quix12345/Q-Flight/qflight/12.png

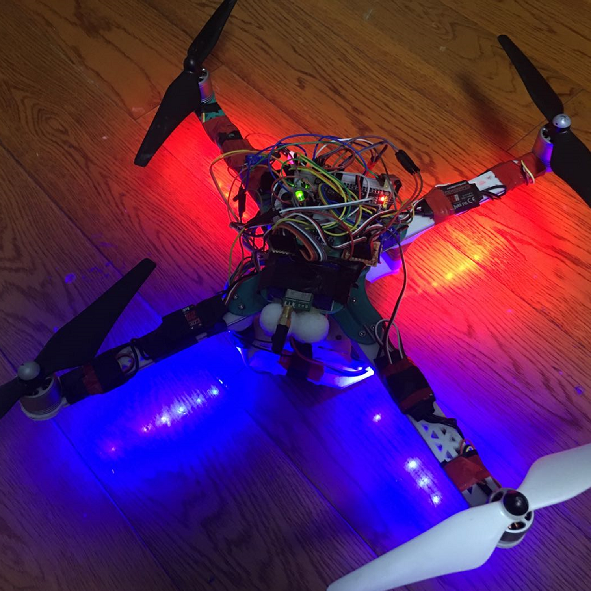
qflight/12.png
