quix12345/Q-Flight/qflight/rc.png

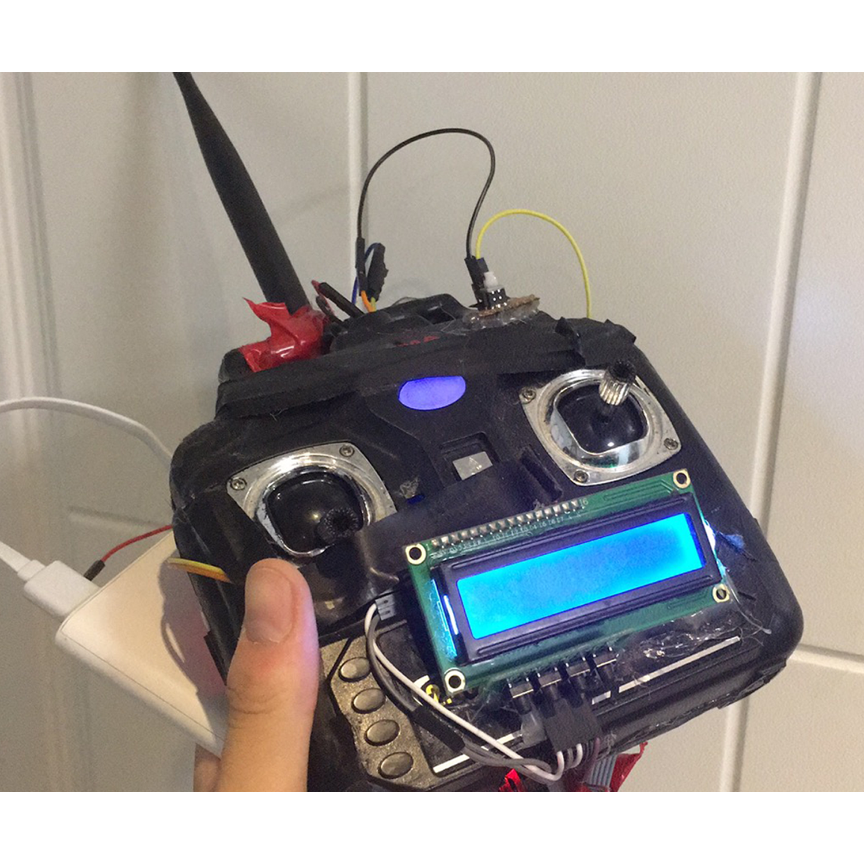
qflight/rc.png
