quix12345/Q-Flight/Models/STL/核心板.STL

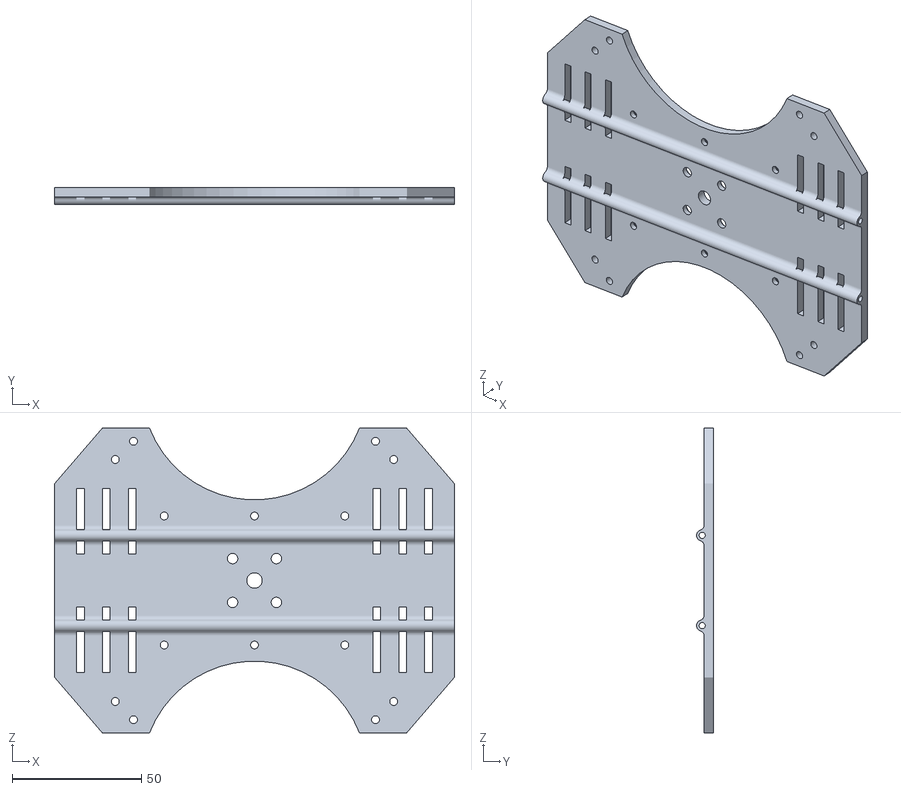
[picture p32: CAD file, 2020-10-18]
Models/STL/核心板.STL
155.0 x 6.55 x 118.0
