quix12345/Q-Flight/Models/Q-Flight version1/减震球.SLDPRT

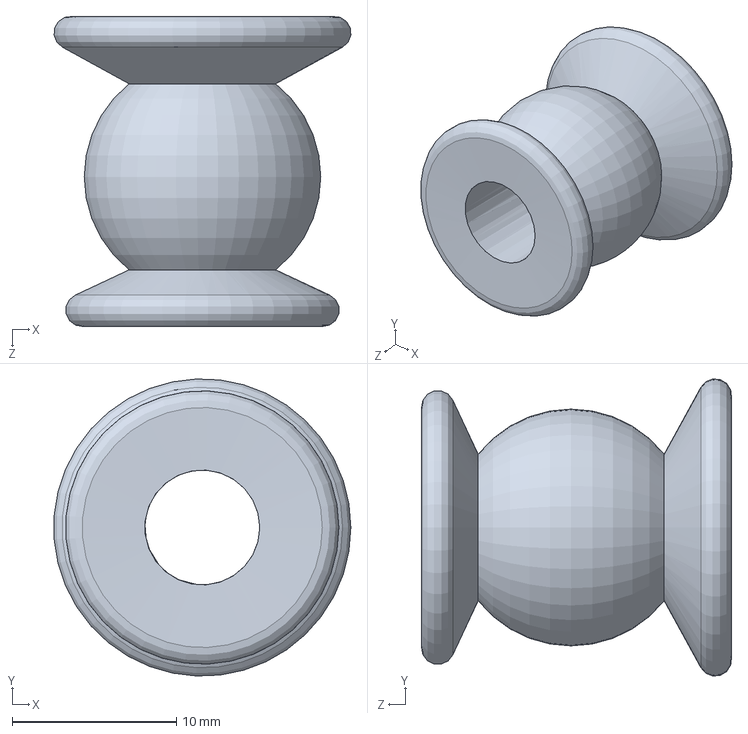
[picture p33: CAD file, 2020-10-18]
Models/Q-Flight version1/减震球.SLDPRT
18.1 x 18.1 x 18.9 mm
