quix12345/Q-Flight/Models/STL/2312圆形电机测试座.STL

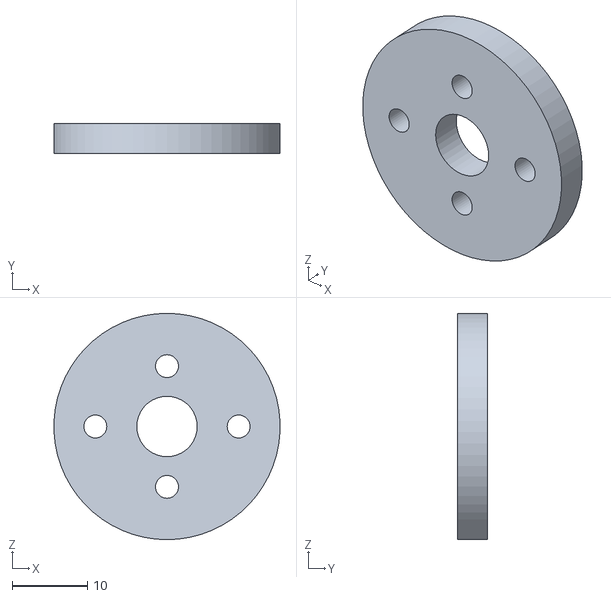
[picture p34: CAD file, 2020-10-18]
Models/STL/2312圆形电机测试座.STL
30.0 x 4.00 x 30.0
