quix12345/Q-Flight/Models/STL/起落架.STL

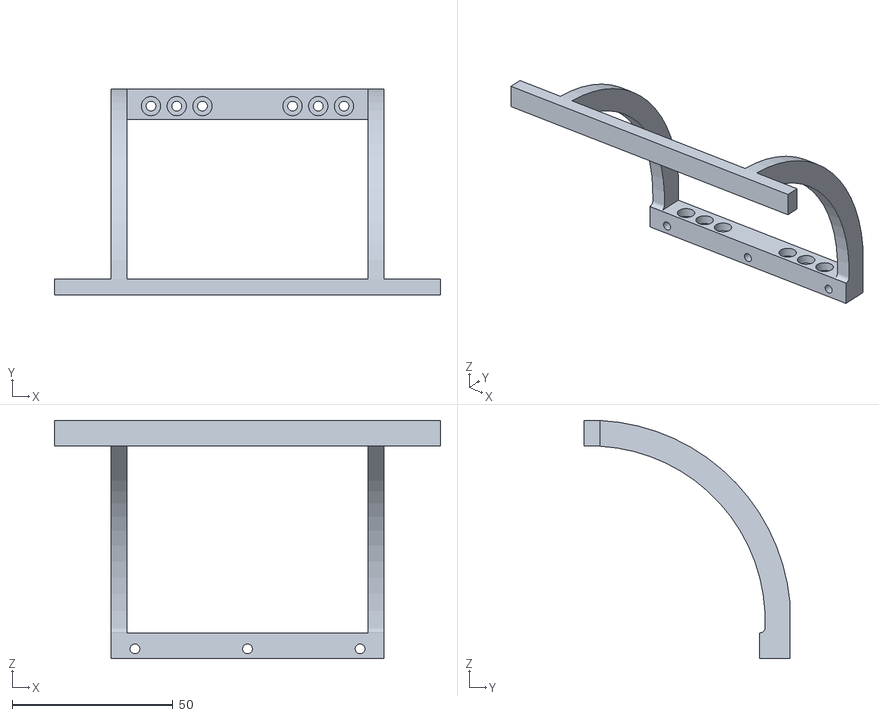
[picture p35: CAD file, 2020-10-18]
Models/STL/起落架.STL
120.0 x 64.0 x 74.0
