quix12345/Q-Flight/Models/Q-Flight version1/航电系统.SLDPRT

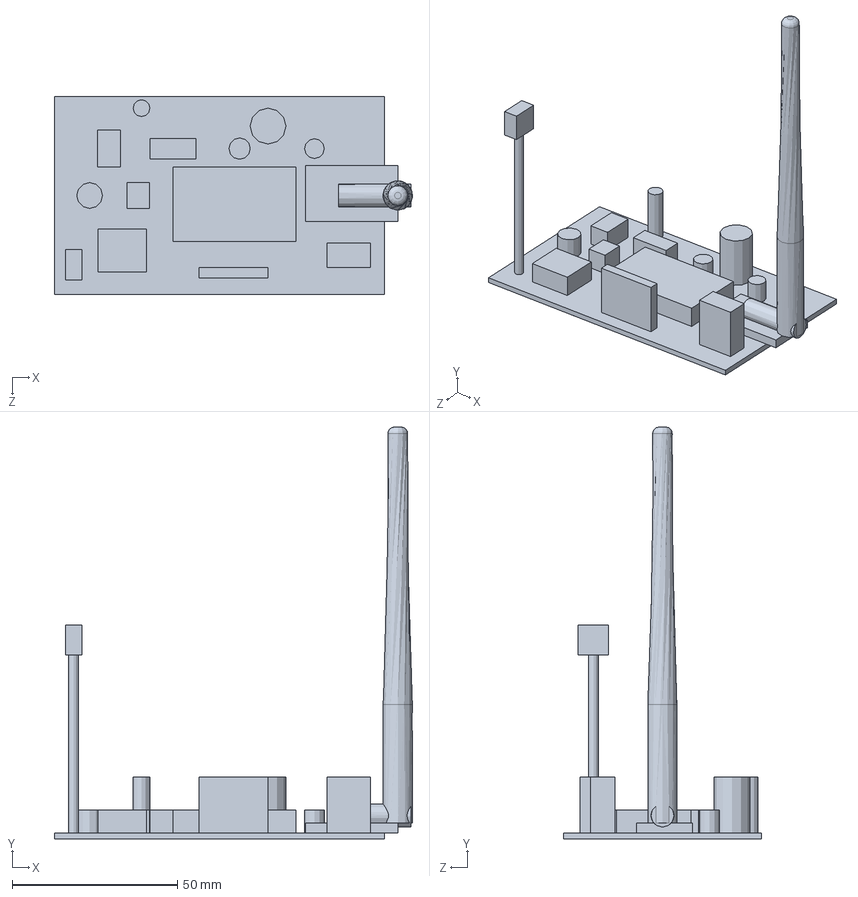
[picture p36: CAD file, 2020-10-18]
Models/Q-Flight version1/航电系统.SLDPRT
108.5 x 124.8 x 60.0 mm
