quix12345/Q-Flight/Models/Q-Flight version1/1047.SLDPRT

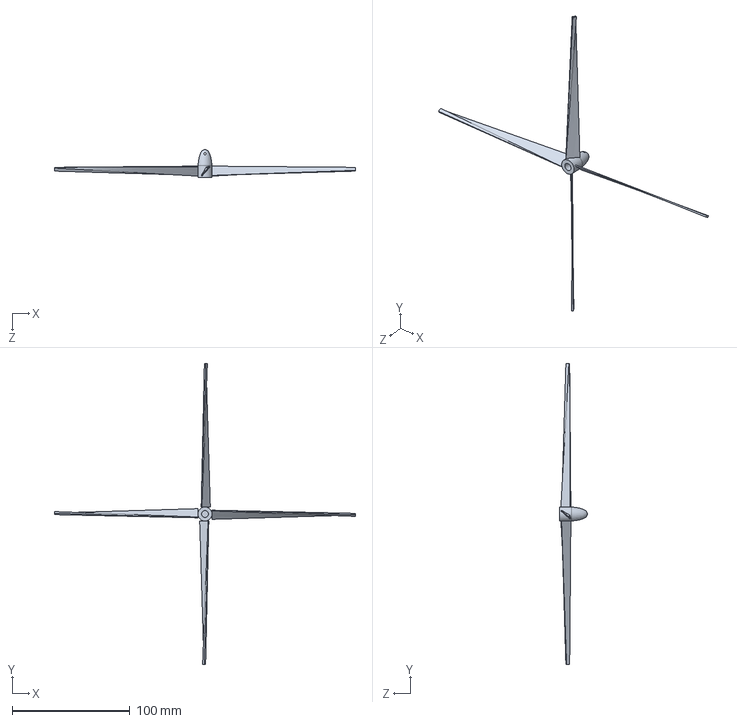
[picture p37: CAD file, 2020-10-18]
Models/Q-Flight version1/1047.SLDPRT
256.0 x 256.0 x 23.5 mm
