quix12345/Q-Flight/Flight_Controller/Q-Flight_F4/main.h

#define REMOTER_USART USART2
#define UART_CONTENT_BUFFER_SIZE 150
#define US_ECHO_Pin GPIO_PIN_1
#define US_ECHO_GPIO_Port GPIOB
#define US_ECHO_EXTI_IRQn EXTI1_IRQn
#define US_TRIG_Pin GPIO_PIN_2
#define US_TRIG_GPIO_Port GPIOB
#define Sensor_Power_Pin GPIO_PIN_10
#define Sensor_Power_GPIO_Port GPIOB
#define NIGHT_LED_Pin GPIO_PIN_14
#define NIGHT_LED_GPIO_Port GPIOB
#define WORK_INDICATE_Pin GPIO_PIN_15
#define WORK_INDICATE_GPIO_Port GPIOB
