quix12345/Q-Flight/Flight_Controller/Q-Flight_F1/Hardware/vl53lxx.c

#include "vl53lxx.h"

float laser_height=0;
uint8_t LaserLidar_enabled=0;

uint8_t VL53L0X_WriteByte(uint8_t reg,uint8_t data)
{
	if(HALIIC_WriteByteToSlave(VL53L0X_ADDR,reg,data))
		return 1;
	else
		return 0;

}

uint8_t VL53L0X_ReadByte(uint8_t reg,uint8_t *buf)
{
	if(HALIIC_ReadByteFromSlave(VL53L0X_ADDR,reg,buf))
		return 1;
	else
		return 0;
}


uint8_t VL53L0X_WriteMultBytes(uint8_t reg,uint8_t len,uint8_t *buf)
{
	if(HALIIC_WriteMultByteToSlave(VL53L0X_ADDR,reg,len,buf))
		return 1;
	else
		return 0;
}

uint8_t VL53L0X_ReadMultBytes(uint8_t reg,uint8_t len,uint8_t *buf)
{
	if(HALIIC_ReadMultByteFromSlave(VL53L0X_ADDR,reg,len,buf))
		return 1;
	else
		return 0;
}

bool VL53L0X_WriteBit(uint8_t addr, uint8_t bitNum, uint8_t data)
{
    uint8_t byte;
    VL53L0X_ReadByte(addr, &byte);
    byte = (data != 0) ? (byte | (1 << bitNum)) : (byte & ~(1 << bitNum));
    VL53L0X_WriteByte(addr, byte);
		return true;
}

static uint16_t io_timeout = 2000;
static uint16_t timeout_start_ms;

// Record the current time to check an upcoming timeout against
#define startTimeout() (timeout_start_ms = HAL_GetTick())

// Check if timeout is enabled (set to nonzero value) and has expired
#define checkTimeoutExpired() (io_timeout > 0 && ((uint16_t)HAL_GetTick() - timeout_start_ms) > io_timeout)

// Decode VCSEL (vertical cavity surface emitting laser) pulse period in PCLKs
// from register value
// based on VL53L0X_decode_vcsel_period()
#define decodeVcselPeriod(reg_val)      (((reg_val) + 1) << 1)

// Encode VCSEL pulse period register value from period in PCLKs
// based on VL53L0X_encode_vcsel_period()
#define encodeVcselPeriod(period_pclks) (((period_pclks) >> 1) - 1)

// Calculate macro period in *nanoseconds* from VCSEL period in PCLKs
// based on VL53L0X_calc_macro_period_ps()
// PLL_period_ps = 1655; macro_period_vclks = 2304
#define calcMacroPeriod(vcsel_period_pclks) ((((uint32_t)2304 * (vcsel_period_pclks) * 1655) + 500) / 1000)

// read by init and used when starting measurement;
// is StopVariable field of VL53L0X_DevData_t structure in API
static uint8_t stop_variable;

static uint32_t measurement_timing_budget_us;
uint16_t measurement_timing_budget_ms;

// Get reference SPAD (single photon avalanche diode) count and type
// based on VL53L0X_get_info_from_device(),
// but only gets reference SPAD count and type
static bool vl53l0xGetSpadInfo(uint8_t * count, bool * type_is_aperture);

// Get sequence step enables
// based on VL53L0X_GetSequenceStepEnables()
static void vl53l0xGetSequenceStepEnables(SequenceStepEnables * enables);

// Get sequence step timeouts
// based on get_sequence_step_timeout(),
// but gets all timeouts instead of just the requested one, and also stores
// intermediate values
static void vl53l0xGetSequenceStepTimeouts(SequenceStepEnables const * enables, SequenceStepTimeouts * timeouts);

// based on VL53L0X_perform_single_ref_calibration()
static bool vl53l0xPerformSingleRefCalibration(uint8_t vhv_init_byte);

// Decode sequence step timeout in MCLKs from register value
// based on VL53L0X_decode_timeout()
// Note: the original function returned a uint32_t, but the return value is
// always stored in a uint16_t.
static uint16_t vl53l0xDecodeTimeout(uint16_t reg_val);

// Encode sequence step timeout register value from timeout in MCLKs
// based on VL53L0X_encode_timeout()
// Note: the original function took a uint16_t, but the argument passed to it
// is always a uint16_t.
static uint16_t vl53l0xEncodeTimeout(uint16_t timeout_mclks);

// Convert sequence step timeout from MCLKs to microseconds with given VCSEL period in PCLKs
// based on VL53L0X_calc_timeout_us()
static uint32_t vl53l0xTimeoutMclksToMicroseconds(uint16_t timeout_period_mclks, uint8_t vcsel_period_pclks);

// Convert sequence step timeout from microseconds to MCLKs with given VCSEL period in PCLKs
// based on VL53L0X_calc_timeout_mclks()
static uint32_t vl53l0xTimeoutMicrosecondsToMclks(uint32_t timeout_period_us, uint8_t vcsel_period_pclks);

static uint16_t vl53l0xReadReg16Bit(uint8_t reg);
static bool vl53l0xWriteReg16Bit(uint8_t reg, uint16_t val);
static bool vl53l0xWriteReg32Bit(uint8_t reg, uint32_t val);


bool vl53l0xTest(void)
{
	bool testStatus;

	testStatus  = vl53l0xTestConnection();
	testStatus &= vl53l0xInitSensor(true);

	return testStatus;
}

void vl53l0xSetParam(void)	/*设置vl53l0x 参数*/
{
	vl53l0xTest();		
	vl53l0xSetVcselPulsePeriod(VcselPeriodPreRange, 18);	/*长距离模式  33ms 周期*/
	vl53l0xSetVcselPulsePeriod(VcselPeriodFinalRange, 14);	/*长距离模式  33ms 周期*/
	vl53l0xStartContinuous(0);
}

/** Verify the I2C connection.
 * Make sure the device is connected and responds as expected.
 * @return True if connection is valid, false otherwise
 */
bool vl53l0xTestConnection(void)
{
  bool ret = true;
  ret &= vl53l0xGetModelID() == VL53L0X_IDENTIFICATION_MODEL_ID;
	HAL_Delay(100);
  ret &= vl53l0xGetRevisionID() == VL53L0X_IDENTIFICATION_REVISION_ID;
  return ret;
}

/** Get Model ID.
 * This register is used to verify the model number of the device,
 * but only before it has been configured to run
 * @return Model ID
 * @see VL53L0X_RA_IDENTIFICATION_MODEL_ID
 * @see VL53L0X_IDENTIFICATION_MODEL_ID
 */
uint16_t vl53l0xGetModelID(void)
{
  return vl53l0xReadReg16Bit(VL53L0X_RA_IDENTIFICATION_MODEL_ID);
}

/** Get Revision ID.
 * This register is used to verify the revision number of the device,
 * but only before it has been configured to run
 * @return Revision ID
 * @see VL53L0X_RA_IDENTIFICATION_REVISION_ID
 * @see VL53L0X_IDENTIFICATION_REVISION_ID
 */
uint8_t vl53l0xGetRevisionID(void)
{
  uint8_t output = 0;
  VL53L0X_ReadByte(VL53L0X_RA_IDENTIFICATION_REVISION_ID, &output);
  return output;
}

// Initialize sensor using sequence based on VL53L0X_DataInit(),
// VL53L0X_StaticInit(), and VL53L0X_PerformRefCalibration().
// This function does not perform reference SPAD calibration
// (VL53L0X_PerformRefSpadManagement()), since the API user manual says that it
// is performed by ST on the bare modules; it seems like that should work well
// enough unless a cover glass is added.
// If io_2v8 (optional) is true or not given, the sensor is configured for 2V8
// mode.
bool vl53l0xInitSensor(bool io_2v8)
{
  uint8_t temp;
  // VL53L0X_DataInit() begin

  // sensor uses 1V8 mode for I/O by default; switch to 2V8 mode if necessary
  if (io_2v8)
  {
    VL53L0X_WriteBit(VL53L0X_RA_VHV_CONFIG_PAD_SCL_SDA__EXTSUP_HV, 0, 0x01);
  }

  // "Set I2C standard mode"
  VL53L0X_WriteByte(0x88, 0x00);

  VL53L0X_WriteByte(0x80, 0x01);
  VL53L0X_WriteByte(0xFF, 0x01);
  VL53L0X_WriteByte(0x00, 0x00);
  VL53L0X_ReadByte(0x91, &stop_variable);
  VL53L0X_WriteByte(0x00, 0x01);
  VL53L0X_WriteByte(0xFF, 0x00);
  VL53L0X_WriteByte(0x80, 0x00);

  // disable SIGNAL_RATE_MSRC (bit 1) and SIGNAL_RATE_PRE_RANGE (bit 4) limit checks
  VL53L0X_ReadByte(VL53L0X_RA_MSRC_CONFIG_CONTROL, &temp);
  VL53L0X_WriteByte(VL53L0X_RA_MSRC_CONFIG_CONTROL, temp | 0x12);

  // set final range signal rate limit to 0.25 MCPS (million counts per second)
  vl53l0xSetSignalRateLimit(0.25);

  VL53L0X_WriteByte(VL53L0X_RA_SYSTEM_SEQUENCE_CONFIG, 0xFF);

  // VL53L0X_DataInit() end

  // VL53L0X_StaticInit() begin

  uint8_t spad_count;
  bool spad_type_is_aperture;
  if (!vl53l0xGetSpadInfo(&spad_count, &spad_type_is_aperture)) { return false; }

  // The SPAD map (RefGoodSpadMap) is read by VL53L0X_get_info_from_device() in
  // the API, but the same data seems to be more easily readable from
  // GLOBAL_CONFIG_SPAD_ENABLES_REF_0 through _6, so read it from there
  uint8_t ref_spad_map[6];
  VL53L0X_ReadMultBytes( VL53L0X_RA_GLOBAL_CONFIG_SPAD_ENABLES_REF_0, 6, ref_spad_map);

  // -- VL53L0X_set_reference_spads() begin (assume NVM values are valid)

  VL53L0X_WriteByte(0xFF, 0x01);
  VL53L0X_WriteByte(VL53L0X_RA_DYNAMIC_SPAD_REF_EN_START_OFFSET, 0x00);
  VL53L0X_WriteByte(VL53L0X_RA_DYNAMIC_SPAD_NUM_REQUESTED_REF_SPAD, 0x2C);
  VL53L0X_WriteByte(0xFF, 0x00);
  VL53L0X_WriteByte(VL53L0X_RA_GLOBAL_CONFIG_REF_EN_START_SELECT, 0xB4);

  uint8_t first_spad_to_enable = spad_type_is_aperture ? 12 : 0; // 12 is the first aperture spad
  uint8_t spads_enabled = 0;

  for (uint8_t i = 0; i < 48; i++)
  {
    if (i < first_spad_to_enable || spads_enabled == spad_count)
    {
      // This bit is lower than the first one that should be enabled, or
      // (reference_spad_count) bits have already been enabled, so zero this bit
      ref_spad_map[i / 8] &= ~(1 << (i % 8));
    }
    else if ((ref_spad_map[i / 8] >> (i % 8)) & 0x1)
    {
      spads_enabled++;
    }
  }

  VL53L0X_WriteMultBytes(VL53L0X_RA_GLOBAL_CONFIG_SPAD_ENABLES_REF_0, 6, ref_spad_map);

  // -- VL53L0X_set_reference_spads() end

  // -- VL53L0X_load_tuning_settings() begin
  // DefaultTuningSettings from vl53l0x_tuning.h

  VL53L0X_WriteByte(0xFF, 0x01);
  VL53L0X_WriteByte(0x00, 0x00);

  VL53L0X_WriteByte(0xFF, 0x00);
  VL53L0X_WriteByte(0x09, 0x00);
  VL53L0X_WriteByte(0x10, 0x00);
  VL53L0X_WriteByte(0x11, 0x00);

  VL53L0X_WriteByte(0x24, 0x01);
  VL53L0X_WriteByte(0x25, 0xFF);
  VL53L0X_WriteByte(0x75, 0x00);

  VL53L0X_WriteByte(0xFF, 0x01);
  VL53L0X_WriteByte(0x4E, 0x2C);
  VL53L0X_WriteByte(0x48, 0x00);
  VL53L0X_WriteByte(0x30, 0x20);

  VL53L0X_WriteByte(0xFF, 0x00);
  VL53L0X_WriteByte(0x30, 0x09);
  VL53L0X_WriteByte(0x54, 0x00);
  VL53L0X_WriteByte(0x31, 0x04);
  VL53L0X_WriteByte(0x32, 0x03);
  VL53L0X_WriteByte(0x40, 0x83);
  VL53L0X_WriteByte(0x46, 0x25);
  VL53L0X_WriteByte(0x60, 0x00);
  VL53L0X_WriteByte(0x27, 0x00);
  VL53L0X_WriteByte(0x50, 0x06);
  VL53L0X_WriteByte(0x51, 0x00);
  VL53L0X_WriteByte(0x52, 0x96);
  VL53L0X_WriteByte(0x56, 0x08);
  VL53L0X_WriteByte(0x57, 0x30);
  VL53L0X_WriteByte(0x61, 0x00);
  VL53L0X_WriteByte(0x62, 0x00);
  VL53L0X_WriteByte(0x64, 0x00);
  VL53L0X_WriteByte(0x65, 0x00);
  VL53L0X_WriteByte(0x66, 0xA0);

  VL53L0X_WriteByte(0xFF, 0x01);
  VL53L0X_WriteByte(0x22, 0x32);
  VL53L0X_WriteByte(0x47, 0x14);
  VL53L0X_WriteByte(0x49, 0xFF);
  VL53L0X_WriteByte(0x4A, 0x00);

  VL53L0X_WriteByte(0xFF, 0x00);
  VL53L0X_WriteByte(0x7A, 0x0A);
  VL53L0X_WriteByte(0x7B, 0x00);
  VL53L0X_WriteByte(0x78, 0x21);

  VL53L0X_WriteByte(0xFF, 0x01);
  VL53L0X_WriteByte(0x23, 0x34);
  VL53L0X_WriteByte(0x42, 0x00);
  VL53L0X_WriteByte(0x44, 0xFF);
  VL53L0X_WriteByte(0x45, 0x26);
  VL53L0X_WriteByte(0x46, 0x05);
  VL53L0X_WriteByte(0x40, 0x40);
  VL53L0X_WriteByte(0x0E, 0x06);
  VL53L0X_WriteByte(0x20, 0x1A);
  VL53L0X_WriteByte(0x43, 0x40);

  VL53L0X_WriteByte(0xFF, 0x00);
  VL53L0X_WriteByte(0x34, 0x03);
  VL53L0X_WriteByte(0x35, 0x44);

  VL53L0X_WriteByte(0xFF, 0x01);
  VL53L0X_WriteByte(0x31, 0x04);
  VL53L0X_WriteByte(0x4B, 0x09);
  VL53L0X_WriteByte(0x4C, 0x05);
  VL53L0X_WriteByte(0x4D, 0x04);

  VL53L0X_WriteByte(0xFF, 0x00);
  VL53L0X_WriteByte(0x44, 0x00);
  VL53L0X_WriteByte(0x45, 0x20);
  VL53L0X_WriteByte(0x47, 0x08);
  VL53L0X_WriteByte(0x48, 0x28);
  VL53L0X_WriteByte(0x67, 0x00);
  VL53L0X_WriteByte(0x70, 0x04);
  VL53L0X_WriteByte(0x71, 0x01);
  VL53L0X_WriteByte(0x72, 0xFE);
  VL53L0X_WriteByte(0x76, 0x00);
  VL53L0X_WriteByte(0x77, 0x00);

  VL53L0X_WriteByte(0xFF, 0x01);
  VL53L0X_WriteByte(0x0D, 0x01);

  VL53L0X_WriteByte(0xFF, 0x00);
  VL53L0X_WriteByte(0x80, 0x01);
  VL53L0X_WriteByte(0x01, 0xF8);

  VL53L0X_WriteByte(0xFF, 0x01);
  VL53L0X_WriteByte(0x8E, 0x01);
  VL53L0X_WriteByte(0x00, 0x01);
  VL53L0X_WriteByte(0xFF, 0x00);
  VL53L0X_WriteByte(0x80, 0x00);

  // -- VL53L0X_load_tuning_settings() end

  // "Set interrupt config to new sample ready"
  // -- VL53L0X_SetGpioConfig() begin

  VL53L0X_WriteByte(VL53L0X_RA_SYSTEM_INTERRUPT_CONFIG_GPIO, 0x04);
  VL53L0X_WriteBit(VL53L0X_RA_GPIO_HV_MUX_ACTIVE_HIGH, 4, 0); // active low
  VL53L0X_WriteByte(VL53L0X_RA_SYSTEM_INTERRUPT_CLEAR, 0x01);

  // -- VL53L0X_SetGpioConfig() end

  measurement_timing_budget_us = vl53l0xGetMeasurementTimingBudget();
  measurement_timing_budget_ms = (uint16_t)(measurement_timing_budget_us / 1000.0f);

  // "Disable MSRC and TCC by default"
  // MSRC = Minimum Signal Rate Check
  // TCC = Target CentreCheck
  // -- VL53L0X_SetSequenceStepEnable() begin

  VL53L0X_WriteByte(VL53L0X_RA_SYSTEM_SEQUENCE_CONFIG, 0xE8);

  // -- VL53L0X_SetSequenceStepEnable() end

  // "Recalculate timing budget"
  vl53l0xSetMeasurementTimingBudget(measurement_timing_budget_us);

  // VL53L0X_StaticInit() end

  // VL53L0X_PerformRefCalibration() begin (VL53L0X_perform_ref_calibration())

  // -- VL53L0X_perform_vhv_calibration() begin

  VL53L0X_WriteByte(VL53L0X_RA_SYSTEM_SEQUENCE_CONFIG, 0x01);
  if (!vl53l0xPerformSingleRefCalibration(0x40)) { printf("Failed VHV calibration\n"); return false; }

  // -- VL53L0X_perform_vhv_calibration() end

  // -- VL53L0X_perform_phase_calibration() begin

  VL53L0X_WriteByte(VL53L0X_RA_SYSTEM_SEQUENCE_CONFIG, 0x02);
  if (!vl53l0xPerformSingleRefCalibration(0x00)) { printf("Failed phase calibration\n"); return false; }

  // -- VL53L0X_perform_phase_calibration() end

  // "restore the previous Sequence Config"
  VL53L0X_WriteByte(VL53L0X_RA_SYSTEM_SEQUENCE_CONFIG, 0xE8);

  // VL53L0X_PerformRefCalibration() end

  return true;
}

// Set the return signal rate limit check value in units of MCPS (mega counts
// per second). "This represents the amplitude of the signal reflected from the
// target and detected by the device"; setting this limit presumably determines
// the minimum measurement necessary for the sensor to report a valid reading.
// Setting a lower limit increases the potential range of the sensor but also
// seems to increase the likelihood of getting an inaccurate reading because of
// unwanted reflections from objects other than the intended target.
// Defaults to 0.25 MCPS as initialized by the ST API and this library.
bool vl53l0xSetSignalRateLimit(float limit_Mcps)
{
  if (limit_Mcps < 0 || limit_Mcps > 511.99f) { return false; }

  // Q9.7 fixed point format (9 integer bits, 7 fractional bits)
  uint16_t fixed_pt = limit_Mcps * (1 << 7);
  return vl53l0xWriteReg16Bit(VL53L0X_RA_FINAL_RANGE_CONFIG_MIN_COUNT_RATE_RTN_LIMIT, fixed_pt);
}

// Set the measurement timing budget in microseconds, which is the time allowed
// for one measurement; the ST API and this library take care of splitting the
// timing budget among the sub-steps in the ranging sequence. A longer timing
// budget allows for more accurate measurements. Increasing the budget by a
// factor of N decreases the range measurement standard deviation by a factor of
// sqrt(N). Defaults to about 33 milliseconds; the minimum is 20 ms.
// based on VL53L0X_set_measurement_timing_budget_micro_seconds()
bool vl53l0xSetMeasurementTimingBudget(uint32_t budget_us)
{
  SequenceStepEnables enables;
  SequenceStepTimeouts timeouts;

  uint16_t const StartOverhead      = 1320; // note that this is different than the value in get_
  uint16_t const EndOverhead        = 960;
  uint16_t const MsrcOverhead       = 660;
  uint16_t const TccOverhead        = 590;
  uint16_t const DssOverhead        = 690;
  uint16_t const PreRangeOverhead   = 660;
  uint16_t const FinalRangeOverhead = 550;

  uint32_t const MinTimingBudget = 20000;

  if (budget_us < MinTimingBudget) { return false; }

  uint32_t used_budget_us = StartOverhead + EndOverhead;

  vl53l0xGetSequenceStepEnables(&enables);
  vl53l0xGetSequenceStepTimeouts(&enables, &timeouts);

  if (enables.tcc)
  {
    used_budget_us += (timeouts.msrc_dss_tcc_us + TccOverhead);
  }

  if (enables.dss)
  {
    used_budget_us += 2 * (timeouts.msrc_dss_tcc_us + DssOverhead);
  }
  else if (enables.msrc)
  {
    used_budget_us += (timeouts.msrc_dss_tcc_us + MsrcOverhead);
  }

  if (enables.pre_range)
  {
    used_budget_us += (timeouts.pre_range_us + PreRangeOverhead);
  }

  if (enables.final_range)
  {
    used_budget_us += FinalRangeOverhead;

    // "Note that the final range timeout is determined by the timing
    // budget and the sum of all other timeouts within the sequence.
    // If there is no room for the final range timeout, then an error
    // will be set. Otherwise the remaining time will be applied to
    // the final range."

    if (used_budget_us > budget_us)
    {
      // "Requested timeout too big."
      return false;
    }

    uint32_t final_range_timeout_us = budget_us - used_budget_us;

    // set_sequence_step_timeout() begin
    // (SequenceStepId == VL53L0X_SEQUENCESTEP_FINAL_RANGE)

    // "For the final range timeout, the pre-range timeout
    //  must be added. To do this both final and pre-range
    //  timeouts must be expressed in macro periods MClks
    //  because they have different vcsel periods."

    uint16_t final_range_timeout_mclks =
      vl53l0xTimeoutMicrosecondsToMclks(final_range_timeout_us,
                                 timeouts.final_range_vcsel_period_pclks);

    if (enables.pre_range)
    {
      final_range_timeout_mclks += timeouts.pre_range_mclks;
    }

    uint16_t temp = vl53l0xEncodeTimeout(final_range_timeout_mclks);
    vl53l0xWriteReg16Bit(VL53L0X_RA_FINAL_RANGE_CONFIG_TIMEOUT_MACROP_HI, temp);

    // set_sequence_step_timeout() end

    measurement_timing_budget_us = budget_us; // store for internal reuse
    measurement_timing_budget_ms = (uint16_t)(measurement_timing_budget_us / 1000.0f);
  }
  return true;
}

// Get the measurement timing budget in microseconds
// based on VL53L0X_get_measurement_timing_budget_micro_seconds()
// in us
uint32_t vl53l0xGetMeasurementTimingBudget(void)
{
  SequenceStepEnables enables;
  SequenceStepTimeouts timeouts;

  uint16_t const StartOverhead     = 1910; // note that this is different than the value in set_
  uint16_t const EndOverhead        = 960;
  uint16_t const MsrcOverhead       = 660;
  uint16_t const TccOverhead        = 590;
  uint16_t const DssOverhead        = 690;
  uint16_t const PreRangeOverhead   = 660;
  uint16_t const FinalRangeOverhead = 550;

  // "Start and end overhead times always present"
  uint32_t budget_us = StartOverhead + EndOverhead;

  vl53l0xGetSequenceStepEnables(&enables);
  vl53l0xGetSequenceStepTimeouts(&enables, &timeouts);

  if (enables.tcc)
  {
    budget_us += (timeouts.msrc_dss_tcc_us + TccOverhead);
  }

  if (enables.dss)
  {
    budget_us += 2 * (timeouts.msrc_dss_tcc_us + DssOverhead);
  }
  else if (enables.msrc)
  {
    budget_us += (timeouts.msrc_dss_tcc_us + MsrcOverhead);
  }

  if (enables.pre_range)
  {
    budget_us += (timeouts.pre_range_us + PreRangeOverhead);
  }

  if (enables.final_range)
  {
    budget_us += (timeouts.final_range_us + FinalRangeOverhead);
  }

  measurement_timing_budget_us = budget_us; // store for internal reuse
  measurement_timing_budget_ms = (uint16_t)(measurement_timing_budget_us / 1000.0f);
  return budget_us;
}


// Set the VCSEL (vertical cavity surface emitting laser) pulse period for the
// given period type (pre-range or final range) to the given value in PCLKs.
// Longer periods seem to increase the potential range of the sensor.
// Valid values are (even numbers only):
//  pre:  12 to 18 (initialized default: 14)
//  final: 8 to 14 (initialized default: 10)
// based on VL53L0X_set_vcsel_pulse_period()
bool vl53l0xSetVcselPulsePeriod(vcselPeriodType type, uint8_t period_pclks)
{
  uint8_t vcsel_period_reg = encodeVcselPeriod(period_pclks);

  SequenceStepEnables enables;
  SequenceStepTimeouts timeouts;

  vl53l0xGetSequenceStepEnables(&enables);
  vl53l0xGetSequenceStepTimeouts(&enables, &timeouts);

  // "Apply specific settings for the requested clock period"
  // "Re-calculate and apply timeouts, in macro periods"

  // "When the VCSEL period for the pre or final range is changed,
  // the corresponding timeout must be read from the device using
  // the current VCSEL period, then the new VCSEL period can be
  // applied. The timeout then must be written back to the device
  // using the new VCSEL period.
  //
  // For the MSRC timeout, the same applies - this timeout being
  // dependant on the pre-range vcsel period."


  if (type == VcselPeriodPreRange)
  {
    // "Set phase check limits"
    switch (period_pclks)
    {
      case 12:
        VL53L0X_WriteByte(VL53L0X_RA_PRE_RANGE_CONFIG_VALID_PHASE_HIGH, 0x18);
        break;

      case 14:
        VL53L0X_WriteByte(VL53L0X_RA_PRE_RANGE_CONFIG_VALID_PHASE_HIGH, 0x30);
        break;

      case 16:
        VL53L0X_WriteByte(VL53L0X_RA_PRE_RANGE_CONFIG_VALID_PHASE_HIGH, 0x40);
        break;

      case 18:
        VL53L0X_WriteByte(VL53L0X_RA_PRE_RANGE_CONFIG_VALID_PHASE_HIGH, 0x50);
        break;

      default:
        // invalid period
        return false;
    }
    VL53L0X_WriteByte(VL53L0X_RA_PRE_RANGE_CONFIG_VALID_PHASE_LOW, 0x08);

    // apply new VCSEL period
    VL53L0X_WriteByte(VL53L0X_RA_PRE_RANGE_CONFIG_VCSEL_PERIOD, vcsel_period_reg);

    // update timeouts

    // set_sequence_step_timeout() begin
    // (SequenceStepId == VL53L0X_SEQUENCESTEP_PRE_RANGE)

    uint16_t new_pre_range_timeout_mclks =
      vl53l0xTimeoutMicrosecondsToMclks(timeouts.pre_range_us, period_pclks);

    uint16_t new_pre_range_timeout_encoded = vl53l0xEncodeTimeout(new_pre_range_timeout_mclks);
    vl53l0xWriteReg16Bit(VL53L0X_RA_PRE_RANGE_CONFIG_TIMEOUT_MACROP_HI, new_pre_range_timeout_encoded);

    // set_sequence_step_timeout() end

    // set_sequence_step_timeout() begin
    // (SequenceStepId == VL53L0X_SEQUENCESTEP_MSRC)

    uint16_t new_msrc_timeout_mclks =
      vl53l0xTimeoutMicrosecondsToMclks(timeouts.msrc_dss_tcc_us, period_pclks);

    VL53L0X_WriteByte(VL53L0X_RA_MSRC_CONFIG_TIMEOUT_MACROP,
      (new_msrc_timeout_mclks > 256) ? 255 : (new_msrc_timeout_mclks - 1));

    // set_sequence_step_timeout() end
  }
  else if (type == VcselPeriodFinalRange)
  {
    switch (period_pclks)
    {
      case 8:
        VL53L0X_WriteByte(VL53L0X_RA_FINAL_RANGE_CONFIG_VALID_PHASE_HIGH, 0x10);
        VL53L0X_WriteByte(VL53L0X_RA_FINAL_RANGE_CONFIG_VALID_PHASE_LOW,  0x08);
        VL53L0X_WriteByte(VL53L0X_RA_GLOBAL_CONFIG_VCSEL_WIDTH, 0x02);
        VL53L0X_WriteByte(VL53L0X_RA_ALGO_PHASECAL_CONFIG_TIMEOUT, 0x0C);
        VL53L0X_WriteByte(0xFF, 0x01);
        VL53L0X_WriteByte(VL53L0X_RA_ALGO_PHASECAL_LIM, 0x30);
        VL53L0X_WriteByte(0xFF, 0x00);
        break;

      case 10:
        VL53L0X_WriteByte(VL53L0X_RA_FINAL_RANGE_CONFIG_VALID_PHASE_HIGH, 0x28);
        VL53L0X_WriteByte(VL53L0X_RA_FINAL_RANGE_CONFIG_VALID_PHASE_LOW,  0x08);
        VL53L0X_WriteByte(VL53L0X_RA_GLOBAL_CONFIG_VCSEL_WIDTH, 0x03);
        VL53L0X_WriteByte(VL53L0X_RA_ALGO_PHASECAL_CONFIG_TIMEOUT, 0x09);
        VL53L0X_WriteByte(0xFF, 0x01);
        VL53L0X_WriteByte(VL53L0X_RA_ALGO_PHASECAL_LIM, 0x20);
        VL53L0X_WriteByte(0xFF, 0x00);
        break;

      case 12:
        VL53L0X_WriteByte(VL53L0X_RA_FINAL_RANGE_CONFIG_VALID_PHASE_HIGH, 0x38);
        VL53L0X_WriteByte(VL53L0X_RA_FINAL_RANGE_CONFIG_VALID_PHASE_LOW,  0x08);
        VL53L0X_WriteByte(VL53L0X_RA_GLOBAL_CONFIG_VCSEL_WIDTH, 0x03);
        VL53L0X_WriteByte(VL53L0X_RA_ALGO_PHASECAL_CONFIG_TIMEOUT, 0x08);
        VL53L0X_WriteByte(0xFF, 0x01);
        VL53L0X_WriteByte(VL53L0X_RA_ALGO_PHASECAL_LIM, 0x20);
        VL53L0X_WriteByte(0xFF, 0x00);
        break;

      case 14:
        VL53L0X_WriteByte(VL53L0X_RA_FINAL_RANGE_CONFIG_VALID_PHASE_HIGH, 0x48);
        VL53L0X_WriteByte(VL53L0X_RA_FINAL_RANGE_CONFIG_VALID_PHASE_LOW,  0x08);
        VL53L0X_WriteByte(VL53L0X_RA_GLOBAL_CONFIG_VCSEL_WIDTH, 0x03);
        VL53L0X_WriteByte(VL53L0X_RA_ALGO_PHASECAL_CONFIG_TIMEOUT, 0x07);
        VL53L0X_WriteByte(0xFF, 0x01);
        VL53L0X_WriteByte(VL53L0X_RA_ALGO_PHASECAL_LIM, 0x20);
        VL53L0X_WriteByte(0xFF, 0x00);
        break;

      default:
        // invalid period
        return false;
    }

    // apply new VCSEL period
    VL53L0X_WriteByte(VL53L0X_RA_FINAL_RANGE_CONFIG_VCSEL_PERIOD, vcsel_period_reg);

    // update timeouts

    // set_sequence_step_timeout() begin
    // (SequenceStepId == VL53L0X_SEQUENCESTEP_FINAL_RANGE)

    // "For the final range timeout, the pre-range timeout
    //  must be added. To do this both final and pre-range
    //  timeouts must be expressed in macro periods MClks
    //  because they have different vcsel periods."

    uint16_t new_final_range_timeout_mclks =
      vl53l0xTimeoutMicrosecondsToMclks(timeouts.final_range_us, period_pclks);

    if (enables.pre_range)
    {
      new_final_range_timeout_mclks += timeouts.pre_range_mclks;
    }

    uint16_t new_final_range_timeout_encoded = vl53l0xEncodeTimeout(new_final_range_timeout_mclks);
    vl53l0xWriteReg16Bit(VL53L0X_RA_FINAL_RANGE_CONFIG_TIMEOUT_MACROP_HI, new_final_range_timeout_encoded);

    // set_sequence_step_timeout end
  }
  else
  {
    // invalid type
    return false;
  }

  // "Finally, the timing budget must be re-applied"

  vl53l0xSetMeasurementTimingBudget(measurement_timing_budget_us);

  // "Perform the phase calibration. This is needed after changing on vcsel period."
  // VL53L0X_perform_phase_calibration() begin

  uint8_t sequence_config = 0;
  VL53L0X_ReadByte(VL53L0X_RA_SYSTEM_SEQUENCE_CONFIG, &sequence_config);
  VL53L0X_WriteByte(VL53L0X_RA_SYSTEM_SEQUENCE_CONFIG, 0x02);
  bool ret = vl53l0xPerformSingleRefCalibration(0x0);
  VL53L0X_WriteByte(VL53L0X_RA_SYSTEM_SEQUENCE_CONFIG, sequence_config);

  // VL53L0X_perform_phase_calibration() end

  return ret;
}

// Get the VCSEL pulse period in PCLKs for the given period type.
// based on VL53L0X_get_vcsel_pulse_period()
uint8_t vl53l0xGetVcselPulsePeriod(vcselPeriodType type)
{
  if (type == VcselPeriodPreRange)
  {
    uint8_t temp = 0;
    VL53L0X_ReadByte(VL53L0X_RA_PRE_RANGE_CONFIG_VCSEL_PERIOD, &temp);
    return decodeVcselPeriod(temp);
  }
  else if (type == VcselPeriodFinalRange)
  {
    uint8_t temp = 0;
    VL53L0X_ReadByte(VL53L0X_RA_FINAL_RANGE_CONFIG_VCSEL_PERIOD, &temp);
    return decodeVcselPeriod(temp);
  }
  else { return 255; }
}

// Start continuous ranging measurements. If period_ms (optional) is 0 or not
// given, continuous back-to-back mode is used (the sensor takes measurements as
// often as possible); otherwise, continuous timed mode is used, with the given
// inter-measurement period in milliseconds determining how often the sensor
// takes a measurement.
// based on VL53L0X_StartMeasurement()
void vl53l0xStartContinuous(uint32_t period_ms)
{
  VL53L0X_WriteByte(0x80, 0x01);
  VL53L0X_WriteByte(0xFF, 0x01);
  VL53L0X_WriteByte(0x00, 0x00);
  VL53L0X_WriteByte(0x91, stop_variable);
  VL53L0X_WriteByte(0x00, 0x01);
  VL53L0X_WriteByte(0xFF, 0x00);
  VL53L0X_WriteByte(0x80, 0x00);

  if (period_ms != 0)
  {
    // continuous timed mode

    // VL53L0X_SetInterMeasurementPeriodMilliSeconds() begin

    uint16_t osc_calibrate_val = vl53l0xReadReg16Bit(VL53L0X_RA_OSC_CALIBRATE_VAL);

    if (osc_calibrate_val != 0)
    {
      period_ms *= osc_calibrate_val;
    }

    vl53l0xWriteReg32Bit(VL53L0X_RA_SYSTEM_INTERMEASUREMENT_PERIOD, period_ms);

    // VL53L0X_SetInterMeasurementPeriodMilliSeconds() end

    VL53L0X_WriteByte(VL53L0X_RA_SYSRANGE_START, 0x04); // VL53L0X_REG_SYSRANGE_MODE_TIMED
  }
  else
  {
    // continuous back-to-back mode
    VL53L0X_WriteByte(VL53L0X_RA_SYSRANGE_START, 0x02); // VL53L0X_REG_SYSRANGE_MODE_BACKTOBACK
  }
}

// Stop continuous measurements
// based on VL53L0X_StopMeasurement()
void vl53l0xStopContinuous(void)
{
  VL53L0X_WriteByte(VL53L0X_RA_SYSRANGE_START, 0x01); // VL53L0X_REG_SYSRANGE_MODE_SINGLESHOT

  VL53L0X_WriteByte(0xFF, 0x01);
  VL53L0X_WriteByte(0x00, 0x00);
  VL53L0X_WriteByte(0x91, 0x00);
  VL53L0X_WriteByte(0x00, 0x01);
  VL53L0X_WriteByte(0xFF, 0x00);
}

// Returns a range reading in millimeters when continuous mode is active
// (readRangeSingleMillimeters() also calls this function after starting a
// single-shot range measurement)
uint16_t vl53l0xReadRangeContinuousMillimeters(void)
{
  startTimeout();
  uint8_t val = 0;
  while ((val & 0x07) == 0)
  {
    VL53L0X_ReadByte(VL53L0X_RA_RESULT_INTERRUPT_STATUS, &val);
    if ((val & 0x07) == 0)
    {
      // Relaxation delay when polling interrupt
      HAL_Delay(1);
    }
    if (checkTimeoutExpired())
    {
      return 65535;
    }
  }

  // assumptions: Linearity Corrective Gain is 1000 (default);
  // fractional ranging is not enabled
  uint16_t range = vl53l0xReadReg16Bit(VL53L0X_RA_RESULT_RANGE_STATUS + 10);

  VL53L0X_WriteByte(VL53L0X_RA_SYSTEM_INTERRUPT_CLEAR, 0x01);

  return range;
}

// Performs a single-shot range measurement and returns the reading in
// millimeters
// based on VL53L0X_PerformSingleRangingMeasurement()
uint16_t vl53l0xReadRangeSingleMillimeters(void)
{
  VL53L0X_WriteByte(0x80, 0x01);
  VL53L0X_WriteByte(0xFF, 0x01);
  VL53L0X_WriteByte(0x00, 0x00);
  VL53L0X_WriteByte(0x91, stop_variable);
  VL53L0X_WriteByte(0x00, 0x01);
  VL53L0X_WriteByte(0xFF, 0x00);
  VL53L0X_WriteByte(0x80, 0x00);

  VL53L0X_WriteByte(VL53L0X_RA_SYSRANGE_START, 0x01);

  // "Wait until start bit has been cleared"
  startTimeout();
  uint8_t val = 0x01;
  while (val & 0x01)
  {
    VL53L0X_ReadByte(VL53L0X_RA_SYSRANGE_START, &val);
    if (checkTimeoutExpired())
    {
      return 65535;
    }
  }

  return vl53l0xReadRangeContinuousMillimeters();
}

// Get reference SPAD (single photon avalanche diode) count and type
// based on VL53L0X_get_info_from_device(),
// but only gets reference SPAD count and type
bool vl53l0xGetSpadInfo(uint8_t * count, bool * type_is_aperture)
{
  uint8_t tmp;

  VL53L0X_WriteByte(0x80, 0x01);
  VL53L0X_WriteByte(0xFF, 0x01);
  VL53L0X_WriteByte(0x00, 0x00);

  VL53L0X_WriteByte(0xFF, 0x06);
  VL53L0X_WriteBit(0x83, 2, 0x01);
  VL53L0X_WriteByte(0xFF, 0x07);
  VL53L0X_WriteByte(0x81, 0x01);

  VL53L0X_WriteByte(0x80, 0x01);

  VL53L0X_WriteByte(0x94, 0x6b);
  VL53L0X_WriteByte(0x83, 0x00);
  startTimeout();

  uint8_t val = 0x00;
  while (val == 0x00) {
    VL53L0X_ReadByte(0x83, &val);
    if (checkTimeoutExpired()) { return false; }
  };
  VL53L0X_WriteByte(0x83, 0x01);
  VL53L0X_ReadByte(0x92, &tmp);

  *count = tmp & 0x7f;
  *type_is_aperture = (tmp >> 7) & 0x01;

  VL53L0X_WriteByte(0x81, 0x00);
  VL53L0X_WriteByte(0xFF, 0x06);
  VL53L0X_WriteBit(0x83, 2, 0);
  VL53L0X_WriteByte(0xFF, 0x01);
  VL53L0X_WriteByte(0x00, 0x01);

  VL53L0X_WriteByte(0xFF, 0x00);
  VL53L0X_WriteByte(0x80, 0x00);

  return true;
}

// Get sequence step enables
// based on VL53L0X_GetSequenceStepEnables()
void vl53l0xGetSequenceStepEnables(SequenceStepEnables * enables)
{
  uint8_t sequence_config = 0;
  VL53L0X_ReadByte(VL53L0X_RA_SYSTEM_SEQUENCE_CONFIG, &sequence_config);

  enables->tcc          = (sequence_config >> 4) & 0x1;
  enables->dss          = (sequence_config >> 3) & 0x1;
  enables->msrc         = (sequence_config >> 2) & 0x1;
  enables->pre_range    = (sequence_config >> 6) & 0x1;
  enables->final_range  = (sequence_config >> 7) & 0x1;
}

// Get sequence step timeouts
// based on get_sequence_step_timeout(),
// but gets all timeouts instead of just the requested one, and also stores
// intermediate values
void vl53l0xGetSequenceStepTimeouts(SequenceStepEnables const * enables, SequenceStepTimeouts * timeouts)
{
  timeouts->pre_range_vcsel_period_pclks = vl53l0xGetVcselPulsePeriod(VcselPeriodPreRange);

  uint8_t temp = 0;
  VL53L0X_ReadByte(VL53L0X_RA_MSRC_CONFIG_TIMEOUT_MACROP, &temp);
  timeouts->msrc_dss_tcc_mclks = temp + 1;
  timeouts->msrc_dss_tcc_us =
    vl53l0xTimeoutMclksToMicroseconds(timeouts->msrc_dss_tcc_mclks,
                               timeouts->pre_range_vcsel_period_pclks);

  uint16_t pre_range_encoded = vl53l0xReadReg16Bit(VL53L0X_RA_PRE_RANGE_CONFIG_TIMEOUT_MACROP_HI);
  timeouts->pre_range_mclks = vl53l0xDecodeTimeout(pre_range_encoded);
  timeouts->pre_range_us =
    vl53l0xTimeoutMclksToMicroseconds(timeouts->pre_range_mclks,
                               timeouts->pre_range_vcsel_period_pclks);

  timeouts->final_range_vcsel_period_pclks = vl53l0xGetVcselPulsePeriod(VcselPeriodFinalRange);

  uint16_t final_range_encoded = vl53l0xReadReg16Bit(VL53L0X_RA_FINAL_RANGE_CONFIG_TIMEOUT_MACROP_HI);
  timeouts->final_range_mclks = vl53l0xDecodeTimeout(final_range_encoded);

  if (enables->pre_range)
  {
    timeouts->final_range_mclks -= timeouts->pre_range_mclks;
  }

  timeouts->final_range_us =
    vl53l0xTimeoutMclksToMicroseconds(timeouts->final_range_mclks,
                               timeouts->final_range_vcsel_period_pclks);
}

// Decode sequence step timeout in MCLKs from register value
// based on VL53L0X_decode_timeout()
// Note: the original function returned a uint32_t, but the return value is
// always stored in a uint16_t.
uint16_t vl53l0xDecodeTimeout(uint16_t reg_val)
{
  // format: "(LSByte * 2^MSByte) + 1"
  return (uint16_t)((reg_val & 0x00FF) <<
         (uint16_t)((reg_val & 0xFF00) >> 8)) + 1;
}

// Encode sequence step timeout register value from timeout in MCLKs
// based on VL53L0X_encode_timeout()
// Note: the original function took a uint16_t, but the argument passed to it
// is always a uint16_t.
uint16_t vl53l0xEncodeTimeout(uint16_t timeout_mclks)
{
  // format: "(LSByte * 2^MSByte) + 1"

  uint32_t ls_byte = 0;
  uint16_t ms_byte = 0;

  if (timeout_mclks > 0)
  {
    ls_byte = timeout_mclks - 1;

    while ((ls_byte & 0xFFFFFF00LU) > 0)
    {
      ls_byte >>= 1;
      ms_byte++;
    }

    return (ms_byte << 8) | (ls_byte & 0xFF);
  }
  else { return 0; }
}

// Convert sequence step timeout from MCLKs to microseconds with given VCSEL period in PCLKs
// based on VL53L0X_calc_timeout_us()
uint32_t vl53l0xTimeoutMclksToMicroseconds(uint16_t timeout_period_mclks, uint8_t vcsel_period_pclks)
{
  uint32_t macro_period_ns = calcMacroPeriod(vcsel_period_pclks);

  return ((timeout_period_mclks * macro_period_ns) + (macro_period_ns / 2)) / 1000;
}

// Convert sequence step timeout from microseconds to MCLKs with given VCSEL period in PCLKs
// based on VL53L0X_calc_timeout_mclks()
uint32_t vl53l0xTimeoutMicrosecondsToMclks(uint32_t timeout_period_us, uint8_t vcsel_period_pclks)
{
  uint32_t macro_period_ns = calcMacroPeriod(vcsel_period_pclks);

  return (((timeout_period_us * 1000) + (macro_period_ns / 2)) / macro_period_ns);
}

// based on VL53L0X_perform_single_ref_calibration()
bool vl53l0xPerformSingleRefCalibration(uint8_t vhv_init_byte)
{
  VL53L0X_WriteByte(VL53L0X_RA_SYSRANGE_START, 0x01 | vhv_init_byte); // VL53L0X_REG_SYSRANGE_MODE_START_STOP

  startTimeout();
  uint8_t temp = 0x00;
  while ((temp & 0x07) == 0)
  {
    VL53L0X_ReadByte(VL53L0X_RA_RESULT_INTERRUPT_STATUS, &temp);
    if (checkTimeoutExpired()) { return false; }
  }

  VL53L0X_WriteByte(VL53L0X_RA_SYSTEM_INTERRUPT_CLEAR, 0x01);

  VL53L0X_WriteByte(VL53L0X_RA_SYSRANGE_START, 0x00);

  return true;
}

uint16_t vl53l0xReadReg16Bit(uint8_t reg)
{
  uint8_t buffer[2] = {0};
  VL53L0X_ReadMultBytes( reg, 2, buffer);
  return ((uint16_t)(buffer[0]) << 8) | buffer[1];
}

bool vl53l0xWriteReg16Bit(uint8_t reg, uint16_t val)
{
  uint8_t buffer[2] = {0};
  buffer[0] = ((val >> 8) & 0xFF);
  buffer[1] = ((val     ) & 0xFF);
  VL53L0X_WriteMultBytes(reg, 2, buffer);
  return true;
}

bool vl53l0xWriteReg32Bit(uint8_t reg, uint32_t val)
{
  uint8_t buffer[4] = {0};
  buffer[0] = ((val >> 24) & 0xFF);
  buffer[1] = ((val >> 16) & 0xFF);
  buffer[2] = ((val >>  8) & 0xFF);
  buffer[3] = ((val      ) & 0xFF);
  VL53L0X_WriteMultBytes(reg, 4, buffer);
  return true;
}

void vl53l0x_Init(){
	bool status = vl53l0xTestConnection();
	if(!status){
		printf("vl5310 error!\r\n");
		HAL_NVIC_SystemReset();
	}
	vl53l0xInitSensor(true);
	vl53l0xSetVcselPulsePeriod(VcselPeriodPreRange, 18);	/*长距离模式  33ms 周期*/
	vl53l0xSetVcselPulsePeriod(VcselPeriodFinalRange, 14);	/*长距离模式  33ms 周期*/
	vl53l0xStartContinuous(0);
}

void vl53l0x_StateMachine(){
	static uint8_t cnt=3;
	if(--cnt<=0){
		cnt=3;
		vl5310x_Update();
	}
}

void vl5310x_Update(){
	// 输出cm
	laser_height=vl53l0xReadRangeContinuousMillimeters() * 0.1f;
	if(laser_height>=300){
		laser_height=-1;
		LaserLidar_enabled=0;
	}
	else{
		laser_height=constrainf(laser_height,0,300);
		if(Cos_Pitch!=0&&Cos_Roll!=0){
			laser_height=laser_height*Cos_Pitch*Cos_Roll; 
		}
		LaserLidar_enabled=1;
	}
}
