quix12345/Q-Flight/Flight_Controller/Q-Flight_F1/Src/i2c.c

/**
  ******************************************************************************
  * File Name          : I2C.c
  * Description        : This file provides code for the configuration
  *                      of the I2C instances.
  ******************************************************************************
  * @attention
  *
  * <h2><center>&copy; Copyright (c) 2020 STMicroelectronics.
  * All rights reserved.</center></h2>
  *
  * This software component is licensed by ST under BSD 3-Clause license,
  * the "License"; You may not use this file except in compliance with the
  * License. You may obtain a copy of the License at:
  *                        opensource.org/licenses/BSD-3-Clause
  *
  ******************************************************************************
  */

/* Includes ------------------------------------------------------------------*/
#include "i2c.h"

I2C_HandleTypeDef hi2c1;

/* I2C1 init function */
void MX_I2C1_Init(void)
{

  hi2c1.Instance = I2C1;
  hi2c1.Init.ClockSpeed = 100000;
  hi2c1.Init.DutyCycle = I2C_DUTYCYCLE_2;
  hi2c1.Init.OwnAddress1 = 0;
  hi2c1.Init.AddressingMode = I2C_ADDRESSINGMODE_7BIT;
  hi2c1.Init.DualAddressMode = I2C_DUALADDRESS_DISABLE;
  hi2c1.Init.OwnAddress2 = 0;
  hi2c1.Init.GeneralCallMode = I2C_GENERALCALL_DISABLE;
  hi2c1.Init.NoStretchMode = I2C_NOSTRETCH_DISABLE;
  if (HAL_I2C_Init(&hi2c1) != HAL_OK)
  {
    Error_Handler();
  }

}

void HAL_I2C_MspInit(I2C_HandleTypeDef* i2cHandle)
{

  GPIO_InitTypeDef GPIO_InitStruct = {0};
  if(i2cHandle->Instance==I2C1)
  {
  
    __HAL_RCC_GPIOB_CLK_ENABLE();
    /**I2C1 GPIO Configuration    
    PB6     ------> I2C1_SCL
    PB7     ------> I2C1_SDA 
    */
    GPIO_InitStruct.Pin = GPIO_PIN_6|GPIO_PIN_7;
    GPIO_InitStruct.Mode = GPIO_MODE_AF_OD;
    GPIO_InitStruct.Speed = GPIO_SPEED_FREQ_HIGH;
    HAL_GPIO_Init(GPIOB, &GPIO_InitStruct);

    /* I2C1 clock enable */
    __HAL_RCC_I2C1_CLK_ENABLE();

    /* I2C1 interrupt Init */
    HAL_NVIC_SetPriority(I2C1_EV_IRQn, 0, 0);
    HAL_NVIC_EnableIRQ(I2C1_EV_IRQn);
    HAL_NVIC_SetPriority(I2C1_ER_IRQn, 2, 0);
    HAL_NVIC_EnableIRQ(I2C1_ER_IRQn);
  }
}

void HAL_I2C_MspDeInit(I2C_HandleTypeDef* i2cHandle)
{

  if(i2cHandle->Instance==I2C1)
  {
    /* Peripheral clock disable */
    __HAL_RCC_I2C1_CLK_DISABLE();
  
    /**I2C1 GPIO Configuration    
    PB6     ------> I2C1_SCL
    PB7     ------> I2C1_SDA 
    */
    HAL_GPIO_DeInit(GPIOB, GPIO_PIN_6|GPIO_PIN_7);

    /* I2C1 interrupt Deinit */
    HAL_NVIC_DisableIRQ(I2C1_EV_IRQn);
    HAL_NVIC_DisableIRQ(I2C1_ER_IRQn);
  }
} 

/* USER CODE BEGIN 1 */
uint8_t HALIIC_WriteByteToSlave(uint8_t I2C_Addr,uint8_t reg,uint8_t data)
{
  uint8_t  *pData;
  pData = &data;
  return HAL_I2C_Mem_Write(&hi2c1, I2C_Addr, reg, I2C_MEMADD_SIZE_8BIT, pData, 1, 100);
}

uint8_t HALIIC_ReadByteFromSlave(uint8_t I2C_Addr,uint8_t reg,uint8_t *buf)
{
  return HAL_I2C_Mem_Read(&hi2c1, I2C_Addr, reg, I2C_MEMADD_SIZE_8BIT, buf, 1, 100);
}


uint8_t HALIIC_ReadMultByteFromSlave(uint8_t dev, uint8_t reg, uint8_t length, uint8_t *data)
{
  return HAL_I2C_Mem_Read(&hi2c1, dev, reg, I2C_MEMADD_SIZE_8BIT, data, length, 200);
}

uint8_t HALIIC_WriteMultByteToSlave(uint8_t dev, uint8_t reg, uint8_t length, uint8_t* data)
{
  return HAL_I2C_Mem_Write(&hi2c1, dev, reg, I2C_MEMADD_SIZE_8BIT, data, length, 200);
}
/* USER CODE END 1 */

/************************ (C) COPYRIGHT STMicroelectronics *****END OF FILE****/
