quix12345/Q-Flight/Flight_Controller/Q-Flight_F1/Inc/i2c.h

/**
  ******************************************************************************
  * File Name          : I2C.h
  * Description        : This file provides code for the configuration
  *                      of the I2C instances.
  ******************************************************************************
  * @attention
  *
  * <h2><center>&copy; Copyright (c) 2020 STMicroelectronics.
  * All rights reserved.</center></h2>
  *
  * This software component is licensed by ST under BSD 3-Clause license,
  * the "License"; You may not use this file except in compliance with the
  * License. You may obtain a copy of the License at:
  *                        opensource.org/licenses/BSD-3-Clause
  *
  ******************************************************************************
  */
/* Define to prevent recursive inclusion -------------------------------------*/
#ifndef __i2c_H
#define __i2c_H
#ifdef __cplusplus
 extern "C" {
#endif

/* Includes ------------------------------------------------------------------*/
#include "main.h"

extern I2C_HandleTypeDef hi2c1;

/* USER CODE BEGIN Private defines */
extern uint8_t HALIIC_WriteMultByteToSlave(uint8_t dev, uint8_t reg, uint8_t length, uint8_t* data);
extern uint8_t HALIIC_WriteByteToSlave(uint8_t I2C_Addr,uint8_t reg,uint8_t data);
extern uint8_t HALIIC_ReadByteFromSlave(uint8_t I2C_Addr,uint8_t reg,uint8_t *buf);
extern uint8_t HALIIC_ReadMultByteFromSlave(uint8_t dev, uint8_t reg, uint8_t length, uint8_t *data);
extern uint8_t HALIIC_WriteMultByteToSlave(uint8_t dev, uint8_t reg, uint8_t length, uint8_t* data);
/* USER CODE END Private defines */

void MX_I2C1_Init(void);

#ifdef __cplusplus
}
#endif
#endif /*__ i2c_H */

/**
  * @}
  */

/**
  * @}
  */

/************************ (C) COPYRIGHT STMicroelectronics *****END OF FILE****/
